nielsverhoeven/magewell-converter-cases/knowledge/neutrik/assets/README.md

# Neutrik drawings and 3D models (third-party assets)

Downloaded on 2026-09-07 from the public "Downloads" sections of neutrik.com product pages. Copyright Neutrik AG; stored here for engineering reference only (cutout geometry, depth behind panel, connector envelopes). Always use the black `-B` variant of each part in this project.

| File | Part | Source URL |
|---|---|---|
| NE8FDP-drawing.pdf / .dxf, NE8FDP.stp | etherCON NE8FDP(-B) | https://www.neutrik.com/media/8668/download/ne8fdp-3.pdf , https://www.neutrik.com/media/12095/download/ne8fdp-4.dxf , https://www.neutrik.com/media/12094/download/30010088_-_NE8FDP.stp |
| NAUSB-W-drawing.pdf / .dxf, NAUSB-W.stp | USB NAUSB-W(-B) | https://www.neutrik.com/media/8974/download/nausb-w-2.pdf , https://www.neutrik.com/media/12188/download/nausb-w-3.dxf , https://www.neutrik.com/media/16360/download/3D%20File%20NAUSB-W-A.stp |
| NAHDMI-W-drawing.pdf / .dxf, NAHDMI-W.stp | HDMI NAHDMI-W(-B) | https://www.neutrik.com/media/8976/download/Drawing%20NAHDMI-W.pdf , https://www.neutrik.com/media/12191/download/Drawing%20NAHDMI-W.dxf , https://www.neutrik.com/media/12190/download/nahdmi.stp |
| NBB75DFG-drawing.pdf / .dxf | BNC NBB75DFG(B) | https://www.neutrik.com/media/8619/download/nbb75dfg-2.pdf , https://www.neutrik.com/media/12043/download/nbb75dfg-3.dxf |
| NBB75DFI.stp | BNC isolated NBB75DFI(B) | https://www.neutrik.com/media/12639/download/3-d-nbb75dfi.stp |
| DBA-BL-drawing.pdf, DBA-BL.stp | Blanking plate DBA-BL(-B) | https://www.neutrik.com/media/8479/download/dba-2.pdf , https://www.neutrik.com/media/19043/download/3D%20Model%20dba-bl.stp |
| NZPF-z-panel-frame-assembly.pdf | Z-panel rack frame assembly instruction (NOT the D cutout standard; kept for reference only) | https://www.neutrik.com/media/8082/download/d-shape-z-panel.pdf |

The D-size cutout dimensions are on each connector drawing (panel cutout view). STEP files open in FreeCAD; convert to STL to use as a ghost body in OpenSCAD (see the `openscad-render` skill).
