nielsverhoeven/magewell-converter-cases/docs/plans/2026-09-28-wide-dovetail.md

# Plan A — wide dovetail with lock (rev 2), post-D34/D35 baseline

> **Implemented as amended by the architect verdict appended at the end of this file (B1–B17 and Amendment 1). Where they conflict, the verdict wins. §6 (lock) is informational only.**

Status: draft, NOT yet architect-validated. Route through `solution-architect` before any developer
starts.

Repo state: `main` @ `047902e`. Rev 2 supersedes rev 1 entirely (same file, overwritten) per user
decisions of 2026-09-28, relayed by the teamlead. **Section 6 (the lock) is a deliberate placeholder**
— do not implement it; the teamlead will resume this plan once a parallel researcher's analysis of
Christopher's DP48 STEP files lands.

**User decisions this revision implements:**
1. Coupling stays the dovetail, with an added lock. No thumbscrews.
2. Width: intermediate, dovetail root width in the 60–70 mm range — value picked and justified below.
3. Drop `fishtail_reserve` AND `case_tripod_insert` (the D35 boss is already gone; this retires the
   reservation too) so the rail can cover the floor centre.
4. Clearance ≥ 0.5 mm on every non-bearing surface: flanks (0.57735 mm horizontal, unchanged from rev
   1) **and now also the groove roof** (taper top vs. groove ceiling) — rev 1's "0 mm roof gap is
   fine" call is overridden by explicit user instruction.
5. Place the rail near the device/case centre of mass in Y (R24 roll-moment resistance), re-checked
   against every floor/wall feature, both existing brackets, and the new vertical bracket.
6. Lock: placeholder only, pending DP48 analysis.

---

## 0. Numeric evidence and scope carried over from rev 1, still valid

- The **standoff fix** (§1 below) is unchanged from rev 1: remove `mcc_rail_male()`'s `MCC_FLOOR_T`
  pedestal, `male-local Z = female-local Z` identity, drop `+ MCC_FLOOR_T` from both brackets' mate
  transforms. All of rev 1 §1's reasoning and exact edits still apply and are repeated in §1 below
  with the roof-clearance interaction folded in.
- The **mated-intersection prototype** from rev 1 (a real CGAL/Manifold `intersection()` render
  returning "Current top level object is empty") is still valid evidence for the flank-clearance
  mechanism; re-run at the new width in §7 before treating this plan as verified — the numbers moved,
  the method didn't.
- **Hard-won lesson, repeat:** any manual epsilon-overlap cut in a prototype must grow the shape's
  height, not just translate it (`_mcc_rail_taper_eps()`'s own pattern) — a bare Z-shift produced a
  false non-empty intersection when this was checked in rev 1.

---

## 1. Standoff fix (unchanged from rev 1) + its interaction with the new roof clearance

### 1.1 Remove the pedestal

`mcc_rail_male()` (`lib/mcc/rail.scad:222-236`) unions a `MCC_FLOOR_T`-tall pedestal under the taper.
Delete it; the male becomes just the taper, standing directly on the bracket's flat top face at local
Z=0 (see §4 for why it is now shorter than `MCC_RAIL_DEPTH`, not equal to it).

**Exact edits to `lib/mcc/rail.scad`:**

1. In `mcc_rail_male()`'s `union()`: delete
   `cuboid([len, MCC_RAIL_MOUTH_W, MCC_FLOOR_T], anchor = BOTTOM);` entirely, and change
   `translate([0, 0, MCC_FLOOR_T]) _mcc_rail_taper(len);` to just calling the taper at Z=0 with the
   new, shorter male height (§4 gives the exact call).
2. `_mcc_rail_flank_extrude(z0, z1)`: change `zb = MCC_FLOOR_T;` to `zb = 0;`, with a comment that the
   "straight" branch now only ever fires for a leg reaching *down* into the consumer's plate
   (`z0 < 0`), since the pedestal segment it used to represent no longer exists.
3. `mcc_rail_female_cut()`'s notch: delete the `translate([0, 0, -MCC_FLOOR_T])` wrapper (was
   compensating for the old `male Z = female Z + MCC_FLOOR_T` relationship — now `male Z = female Z`,
   identity, no compensation needed). See §4 for the exact new Z-range (it is not simply
   `[-MCC_EPS, MCC_RAIL_DEPTH]` any more, because of the roof clearance).
4. The latch-height assert (was `MCC_RAIL_SILL_H + plate_t >= 5`): change to reference the male's
   *actual* new height, `MCC_RAIL_MALE_H` (§4) — `MCC_RAIL_SILL_H` (7.0) stays the *case-side* sill
   height (T1-38, unrelated to the bracket) and must not be reused here.
5. Rewrite the stale header block (lines 35-43): no more pedestal/standoff language; state the local
   Z=0 correspondence is direct on both halves, and that the flat case-floor and flat bracket-plate
   faces, everywhere outside the two footprints, sit flush by construction.

**`lib/mcc/mounts.scad` needs no change for the standoff fix** — confirmed again on rev 2: every
`MCC_RAIL_SILL_H` reference there (`mcc_floor_features_add()`'s sill block, the D34 passage's
`pass_h` cap) is already case-side and untouched by the male's own pedestal.

### 1.2 Both bracket mate transforms drop `+ MCC_FLOOR_T`

- **`models/brackets/tv-bracket.scad:236`**: `translate([0, MCC_RAIL_Y, MCC_FLOOR_T]) rotate(...)` →
  `translate([0, MCC_RAIL_Y, 0]) rotate(...)`. Rewrite the "Derivation of the rotate([0,0,180])"
  comment block (lines 39-57) to the simpler, offset-free composition.
- **`models/brackets/arch-tv-bracket.scad`**: see §5 — bound up with the sweep-condition re-derivation,
  not a standalone edit.
- **`models/coupons/rail-latch.scad`**: no edit — it only calls the two public rail functions, so both
  fixes are picked up automatically. Its golden moves (§7).

---

## 2. Retire `fishtail_reserve` and `case_tripod_insert`

### 2.1 What to delete

**`lib/mcc/layout.scad`, `mcc_floor_keepout()`:** delete both rows —
```
[floor_center[0], floor_center[1], "circle", MCC_CASE_INSERT_KEEPOUT_D, "case_tripod_insert"],
[floor_center[0], floor_center[1], "rect", MCC_FISHTAIL_BAND, "fishtail_reserve"],
```
and the now-unused `floor_center = [0, 0]` local (nothing else in this function reads it once both
rows are gone — confirm with a grep before deleting, but tracing the current code, this is its only
use).

**`lib/mcc/mounts.scad`, `mcc_assert_floor_keepout_no_overlap()`:** delete the now-dead exemption
clause for the `"case_tripod_insert"`/`"fishtail_reserve"` pair (D19) — both labels can never appear
in the list again, so the `if (!((rows[i][4] == "case_tripod_insert" && ...) || ...))` wrapper around
the assert becomes unreachable dead code. Simplify back to a plain, unconditional pairwise assert.

**`lib/mcc/constants.scad`:** delete `MCC_CASE_INSERT_KEEPOUT_D` and `MCC_FISHTAIL_BAND` — both become
fully unused once their only consumer (the two rows above) is gone. Verify with
`grep -rn "MCC_CASE_INSERT_KEEPOUT_D\|MCC_FISHTAIL_BAND" lib/ models/ tests/` before deleting; if
either has grown a second consumer since this research pass, stop and report rather than deleting
silently.

### 2.2 `cfg["tripod_insert"]` — recommend assert-incompatible, not full retirement

The D35 boss (`mcc_case_tripod_insert_boss()`/`mcc_tripod_insert_bore_cut()` in `lib/mcc/cradle.scad`,
opt-in via `cfg["tripod_insert"]`, default `false` since D35) is **not itself removed by this plan** —
only the always-on floor *reservation* for it is. Recommendation: **make `tripod_insert=true` and
`rail=true` mutually exclusive by assert**, not delete the boss capability outright.

Reasoning for recommending this over full retirement: nothing currently ships with
`tripod_insert=true` (D35's default is already `false`), so there is no live regression either way.
Deleting the boss/bore modules and their T1-32/T1-41 asserts is real, working, tested code with no
compensating benefit today — it forecloses a genuine future option (a non-bracket-mounted variant that
still wants a floor tripod thread) for zero present gain. An assert is cheap, reversible, and states
the real physical fact plainly: with the rail now covering the floor centre, the two features cannot
coexist. If the architect judges the future-optionality argument not worth carrying, full retirement
(deleting `mcc_case_tripod_insert_boss()`/`_bore_cut()`, their call sites in `cradle.scad`, the
`tripod_insert` cfg key from all 8 `case.scad` files, and `MCC_INSERT_1_4_20` if it becomes unused) is
the documented alternative — flagged for the architect to pick, not silently assumed.

**Exact edit, `lib/mcc/cradle.scad`, `mcc_cradle()`** (where `tripod_on` is read): add, right after the
existing `tripod_on = is_undef(tripod_flag) ? false : tripod_flag;` line —
```
assert(!(tripod_on && struct_val(cfg, "rail") != false),
    "mcc: cfg[\"tripod_insert\"]=true cannot combine with the mount rail (cfg[\"rail\"], default "
    + "true) -- the rail now covers the floor centre the tripod insert boss needs (2026-09-28 "
    + "wide-dovetail decision). Set [\"rail\", false] to use the tripod insert instead.");
```
(`struct_val(cfg, "rail") != false` mirrors the same `is_undef(...) ? true : ...` default the rail
flag itself uses elsewhere, so an *absent* `"rail"` key — which defaults to rail-on — correctly still
trips this assert.)

### 2.3 `CLAUDE.md`'s fixed-decision floor-features line

This file is project-owned prose, not something this plan edits — proposed replacement text for
whoever applies it (the current line is already stale, predating D-15's VESA removal):

> Floor features (one owner, `mounts.scad`): the tool-less dovetail mount rail (default; see §11 D-xx
> for width/placement), strap slots, splitter tie-down, stacking profile. The case's own 1/4"-20
> threaded insert is an **opt-in alternative to the rail**, mutually exclusive with it (assert-guarded,
> `cradle.scad`), not fitted by default. VESA 75×75 (D-15) and Magewell-Fishtail M4 compatibility
> (2026-09-28 wide-dovetail decision) have both been dropped — the rail now needs the floor centre they
> used to reserve.
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
