nielsverhoeven/magewell-converter-cases/tests/test_rail.scad

//////////////////////////////////////////////////////////////////////
// tests/test_rail.scad
//   Tier-2 headless smoke test (architecture.md §9). Instantiates every public module/function in
//   lib/mcc/rail.scad at default (MCC_RAIL_LEN) and short (coupon-scale, len=60) parameters, and
//   exercises the two rev-9 blocking asserts issue #25 introduced:
//     - T1-38 (lib/mcc/rail.scad mcc_rail_female_cut()): >= MCC_FLOOR_T of residual floor over the
//       groove (layout-patch-wall.md §17.2 R1).
//     - D16 (lib/mcc/mounts.scad mcc_assert_floor_keepout_no_overlap()): no two
//       mcc_floor_keepout() rows overlap (no exemptions since D44), run against a real device record.
//     - T1-63.1 .. T1-63.3 (D63.1): the top lock's ride budget, strips and roof lead-in; D50: the
//       rail's plate-side keep-out, mcc_rail_male_keepout().
//     - T1-64.1 (D64.1): the groove's closed -X end keeps a full end wall; T1-17 (D45/D64.1): the rail sill
//       clears the reserved splitter bay, against the tightest SKU (L = 193.9).
//     - T1-62 (D44): >= MCC_RAIL_MATE_CLR normal to the flanks and at the roof.
//   CSG export (-o out.csg) evaluates the full tree so in-model asserts fire, without tessellating.
// Run:
//   openscad --backend=Manifold -o out.csg tests/test_rail.scad
//////////////////////////////////////////////////////////////////////

$fa = 1; $fs = 0.4;

include <mcc/mcc.scad>
include <mcc/devices/pro-convert-for-ndi-to-hdmi.scad>

// --- mcc_rail_sill_size() -- pure function, no geometry ----------------------------------------
_sill = mcc_rail_sill_size();
assert(_sill[0] == MCC_RAIL_LEN + 2 * MCC_RAIL_END_WALL, str("mcc_rail_sill_size len=", _sill[0]));
assert(_sill[1] == MCC_RAIL_ROOT_W + 2 * MCC_RAIL_SILL_SIDE_W, str("mcc_rail_sill_size width=", _sill[1]));
// D30: the sill's side walls beside the groove root must be real walls, not knife edges.
assert(MCC_RAIL_SILL_SIDE_W >= MCC_WALL - MCC_EPS, str("D30: MCC_RAIL_SILL_SIDE_W=", MCC_RAIL_SILL_SIDE_W, " below MCC_WALL"));
assert(_sill[2] == MCC_RAIL_SILL_H, str("mcc_rail_sill_size height=", _sill[2]));

// --- T1-38: MCC_RAIL_SILL_H - MCC_RAIL_DEPTH >= MCC_FLOOR_T, checked directly (not just via the
// module assert, which only fires at render) so a constants.scad regression fails this smoke test
// with a clear message before it ever reaches a full case render. ----------------------------
assert(MCC_RAIL_SILL_H - MCC_RAIL_DEPTH >= MCC_FLOOR_T,
    str("T1-38: MCC_RAIL_SILL_H(", MCC_RAIL_SILL_H, ") - MCC_RAIL_DEPTH(", MCC_RAIL_DEPTH,
        ") must be >= MCC_FLOOR_T(", MCC_FLOOR_T, ")"));

// --- Top lock (D63.1): ride budget, strips and roof lead-in, checked from the constants so a regression
// fails here before any render (T1-63.1 .. T1-63.3, T1-64.1). ----------------------------------------------
assert(abs(mcc_rail_z_play() - MCC_RAIL_MATE_CLR / cos(MCC_RAIL_FLANK_ANGLE)) < 1e-6,
    str("mcc_rail_z_play()=", mcc_rail_z_play()));
assert(MCC_RAIL_LOCK_ENGAGE + MCC_RAIL_LOCK_PLAY_MARGIN <= mcc_rail_z_play() + MCC_EPS,
    str("T1-63.1: lock strip ", MCC_RAIL_LOCK_ENGAGE, " + margin ", MCC_RAIL_LOCK_PLAY_MARGIN,
        " does not fit the Z-play ", mcc_rail_z_play()));
assert(30 <= MCC_RAIL_LOCK_RAMP_IN && MCC_RAIL_LOCK_RAMP_IN <= 60, "T1-63.2: lock entry chamfer outside 30..60 deg");
assert(MCC_RAIL_LOCK_STRIP_Y_OUT <= MCC_RAIL_MOUTH_W / 2 + MCC_RAIL_MALE_H / tan(MCC_RAIL_FLANK_ANGLE) - 1,
    "T1-63.2: lock strips reach within 1 mm of the male's top edge");
assert(MCC_RAIL_LOCK_ENGAGE < MCC_RAIL_LEADIN && MCC_RAIL_LEADIN <= MCC_WALL,
    "T1-63.3: rail lead-in not taller than the lock engagement, or deeper than MCC_WALL");
assert(MCC_RAIL_END_WALL >= MCC_WALL - MCC_EPS, "T1-64.1: the groove's closed end wall is thinner than MCC_WALL");
_slot = mcc_rail_lock_slot();
assert(_slot[1] == [-(MCC_RAIL_ROOT_W / 2 + MCC_RAIL_CLR_HORIZ), MCC_RAIL_ROOT_W / 2 + MCC_RAIL_CLR_HORIZ],
    str("D63.1: the lock slot must span the whole roof, got y=", _slot[1]));
assert(abs(_slot[2][1] - (MCC_RAIL_DEPTH + MCC_RAIL_LOCK_ENGAGE + MCC_RAIL_ROOF_CLR)) < 1e-6,
    str("D63.1: lock slot ceiling z=", _slot[2][1]));

// --- D50: the plate-side keep-out every bracket reads (never the MCC_RAIL_LOCK_* constants) --------
_rail_ko = mcc_rail_male_keepout();
assert(_rail_ko == [[-MCC_RAIL_LEN / 2, MCC_RAIL_LEN / 2],
                    [-MCC_RAIL_ROOT_W / 2, MCC_RAIL_ROOT_W / 2]],
    str("D50: mcc_rail_male_keepout()=", _rail_ko));
assert(mcc_rail_male_keepout(60)[0] == [-30, 30],
    str("D50: mcc_rail_male_keepout(60)=", mcc_rail_male_keepout(60)));

// --- T1-62 / D44: >= MCC_RAIL_MATE_CLR on every non-bearing face, and the user's width range ------
assert(MCC_RAIL_CLR_HORIZ * sin(MCC_RAIL_FLANK_ANGLE) >= MCC_RAIL_MATE_CLR - MCC_EPS,
    str("T1-62: rail flank clearance ", MCC_RAIL_CLR_HORIZ * sin(MCC_RAIL_FLANK_ANGLE), " below ", MCC_RAIL_MATE_CLR));
assert(MCC_RAIL_DEPTH - MCC_RAIL_MALE_H >= MCC_RAIL_MATE_CLR - MCC_EPS,
    str("T1-62: rail roof clearance ", MCC_RAIL_DEPTH - MCC_RAIL_MALE_H, " below ", MCC_RAIL_MATE_CLR));
assert(MCC_RAIL_MATE_CLR >= 0.5 - MCC_EPS, "D44: the user's minimum rail clearance is 0.5 mm");
assert(MCC_RAIL_ROOT_W >= 60 && MCC_RAIL_ROOT_W <= 70,
    str("D44: MCC_RAIL_ROOT_W=", MCC_RAIL_ROOT_W, " outside the user's 60-70 mm range"));

// --- mcc_rail_male() / mcc_rail_female_cut() -- default (production MCC_RAIL_LEN) --------------
translate([0, 0, 0]) mcc_rail_male();
// D50: a consumer unions the rail onto its plate -- the rail needs no cut in the plate.
translate([0, -60, 0])
    union() {
        translate([0, 0, -6]) cuboid([MCC_RAIL_LEN + 10, MCC_RAIL_ROOT_W + 10, 6], anchor = BOTTOM);
        mcc_rail_male();
    }
translate([0, 60, 0])
    difference() {
        cuboid([MCC_RAIL_LEN, MCC_RAIL_ROOT_W + 20, MCC_RAIL_SILL_H], anchor = BOTTOM);
        mcc_rail_female_cut(open_ext = 20, entry_x = MCC_RAIL_LEN / 2);
    }

// --- mcc_rail_male() / mcc_rail_female_cut() -- short, coupon-scale len=60 (models/coupons/
// rail-lock.scad's own length) -- the lock strips must be re-derived from THIS len
// (len/2 - MCC_RAIL_LOCK_END_OFFSET); this is exactly the regression the len=60 case here guards
// against. The e-ladder's largest strip (lock_e = 0.7, M15; T1-63.1's ceiling) must render too, with
// its backing. ------------------------------------------------------------------------------------
translate([200, 0, 0]) mcc_rail_male(len = 60);
translate([200, 60, 0])
    difference() {
        cuboid([60, MCC_RAIL_ROOT_W + 20, MCC_RAIL_SILL_H], anchor = BOTTOM);
        mcc_rail_female_cut(len = 60);
    }
translate([300, 0, 0]) mcc_rail_male(len = 60, lock_e = 0.7);
translate([300, 60, 0])
    difference() {
        union() {
            cuboid([62, MCC_RAIL_ROOT_W + 20, MCC_RAIL_SILL_H], anchor = BOTTOM);
            mcc_rail_female_backing(len = 60, lock_e = 0.7);
        }
        mcc_rail_female_cut(len = 60, open_ext = 1, entry_x = 31, lock_e = 0.7);
    }

// --- D16 / D19 (lib/mcc/mounts.scad): pairwise floor-keepout non-overlap, against a real device
// record and its default variant config, with the mount-rail row now in the list. Emits no
// geometry (pure assert module) -- a bare module-call statement is enough to force evaluation.
DEV = MCC_DEV_PRO_CONVERT_FOR_NDI_TO_HDMI;
VARIANT = [
    ["fan",      false],
    ["splitter", false],
];
mcc_assert_floor_keepout_no_overlap(DEV, VARIANT);

// mcc_floor_keepout()'s own "mount_rail" row, sanity-checked directly (rev 9, D-15).
_ko = mcc_floor_keepout(DEV, VARIANT);
_rail_rows = [for (r = _ko) if (r[4] == "mount_rail") r];
assert(len(_rail_rows) == 1, str("expected exactly one \"mount_rail\" row, got ", len(_rail_rows)));
// D34: the groove runs from its closed end at -MCC_RAIL_LEN/2 out through the +X wall.
_L = struct_val(mcc_case_layout(DEV, VARIANT), "L");
assert(abs(_rail_rows[0][0] - (_L / 2 - MCC_RAIL_LEN / 2) / 2) < 1e-6 && _rail_rows[0][1] == MCC_RAIL_Y,
    str("mount_rail row centre=", [_rail_rows[0][0], _rail_rows[0][1]]));
assert(_rail_rows[0][3] == [_L / 2 + MCC_RAIL_LEN / 2, MCC_RAIL_ROOT_W],
    str("mount_rail row size=", _rail_rows[0][3]));
// No "vesa_*" rows survive (D-15 -- VESA fully removed, not deprecated-but-optional).
_vesa_rows = [for (r = _ko) if (r[4] == "vesa_ne" || r[4] == "vesa_se" || r[4] == "vesa_nw" || r[4] == "vesa_sw") r];
assert(len(_vesa_rows) == 0, str("expected zero VESA rows, got ", len(_vesa_rows)));

// --- mcc_floor_features_add()/mcc_rail_features_cut() -- the shell.scad call-site pair, exercised
// directly (default cfg["rail"]=true) so the ADD/CUT split renders as one clean, watertight block.
translate([400, 0, 0])
    difference() {
        mcc_floor_features_add(DEV, VARIANT);
        mcc_rail_features_cut(DEV, VARIANT);
    }

// cfg["rail"]=false -- both must render (and add/cut) nothing, not error.
translate([400, 60, 0]) {
    mcc_floor_features_add(DEV, [["fan", false], ["splitter", false], ["rail", false]]);
    mcc_rail_features_cut(DEV, [["fan", false], ["splitter", false], ["rail", false]]);
}

echo("mcc test_rail: OK");

// -----------------------------------------------------------------------------------------
// Manual checks: OpenSCAD has no "expect this render to fail" mechanism, so these cannot be
// asserted automatically in a render that must otherwise succeed. To verify a guard by hand,
// append the indicated line to a scratch copy of this file and confirm the render FAILS
// (non-zero exit) with an ERROR containing the quoted text.
//
// 1. T1-38, violated directly by shrinking the constant (constants.scad would need a local
//    override, e.g. via -D, since MCC_RAIL_SILL_H is derived -- simplest is a scratch edit setting
//    MCC_RAIL_SILL_H = MCC_RAIL_DEPTH + 1.0 in constants.scad and re-running this file):
//    -> "T1-38: MCC_RAIL_SILL_H(5) - MCC_RAIL_DEPTH(4) must be >= MCC_FLOOR_T(3)"
//
// 2. D16, violated by moving the rail onto the side-bolt support web (scratch edit constants.scad
//    MCC_RAIL_Y = -40):
//    -> "mcc: floor features \"mount_rail\" and \"side_bolt_web\" overlap ... (D16)"
//
// 3. T1-63 (D44), the opt-in case insert together with the (default-on) rail:
//    mcc_cradle(DEV, [["fan", false], ["splitter", false], ["tripod_insert", true]]);
//    -> "mcc: T1-63 cfg[\"tripod_insert\"]=true needs [\"rail\", false] ..."
//
// 4. T1-63.1 (D63.1), lock strips too tall for the Z-play (scratch edit constants.scad
//    MCC_RAIL_LOCK_ENGAGE = 0.8), then render a case base or the coupon; the render fails with:
//    "mcc: T1-63.1 rail lock strip 0.8 + margin 0.3 does not fit the Z-play 1"
//
// 5. T1-17 (D64.1), the rail sill running into the splitter bay (scratch edit constants.scad
//    MCC_RAIL_LEN = 150.0), then run this file; it fails with:
//    "mcc: T1-17 rail sill -X end x=-78 is within MCC_FAN_BAY_CLR=2 of the reserved splitter bay ..."
// -----------------------------------------------------------------------------------------

// vim: expandtab tabstop=4 shiftwidth=4 softtabstop=4 nowrap
