nielsverhoeven/magewell-converter-cases/tests/test_shell.scad

//////////////////////////////////////////////////////////////////////
// tests/test_shell.scad
//   Tier-2 headless smoke test (architecture.md §9). Instantiates mcc_shell_base()/
//   mcc_shell_lid() (shell.scad), mcc_cradle() (cradle.scad), mcc_floor_features_add/cut()
//   (mounts.scad), and mcc_vents() for each of the 3 vented wall faces (vents.scad), all for
//   MCC_DEV_PRO_CONVERT_FOR_NDI_TO_HDMI — CSG export (-o out.csg) evaluates the full tree so every
//   in-model Tier-1 assert fires, without tessellating. Also exercises the lid vent field (issue
//   #24, T1-36/T1-37) via VARIANT/VARIANT_FAN (lid_vents=true) and VARIANT_NO_LID_VENTS
//   (lid_vents=false).
// Run:
//   openscad --backend=Manifold -o out.csg tests/test_shell.scad
//////////////////////////////////////////////////////////////////////

$fa = 1; $fs = 0.4;

include <mcc/mcc.scad>
include <mcc/devices/pro-convert-for-ndi-to-hdmi.scad>
include <mcc/devices/pro-convert-hdmi-plus.scad>

DEV = MCC_DEV_PRO_CONVERT_FOR_NDI_TO_HDMI;
// "external_ports" is DROPPED from cfg (D12, architecture.md §13 -- inert, never implemented; the
// slot set comes solely from mcc_ports_external(dev)). Real cfg keys only.
VARIANT = [
    ["fan",             false],
    ["splitter",        false],
    ["lid_vents",       true],
];
VARIANT_FAN = [
    ["fan",             true],
    ["splitter",        false],
    // ["fan_switch",false]: the compact family's feasible switch_y interval is EMPTY (D-18,
    // layout-patch-wall.md §18.2) -- without this, T1-43 fails on this SKU's own base_fan golden.
    ["fan_switch",      false],
];

// Fan-switch coverage (rev 11, #32, D-18 §18.4): B6 stops the compact VARIANT_FAN above from
// exercising the switch cutout at all, so without a plus-family branch the feature would ship
// untested by `smoke` (D15's lesson, repeated). DEV_PLUS/VARIANT_PLUS_SWITCH exist ONLY to give
// mcc_switch_cutout()/mcc_switch_pad() and T1-43/T1-44 a real render-time exercise.
DEV_PLUS = MCC_DEV_PRO_CONVERT_HDMI_PLUS;
VARIANT_PLUS_SWITCH = [
    ["fan",             true],
    ["splitter",        false],
    ["fan_switch",      true],
    ["lid_vents",       true],
];
// tripod_insert defaults to false (D35) when the key is absent, as VARIANT/VARIANT_FAN above both
// exercise implicitly. This variant explicitly sets it false, exercising the deck-lattice's
// tripod_insert=false path (issue #29) -- the boss and its collar/bore-cut are omitted entirely.
VARIANT_NO_TRIPOD = concat(VARIANT, [["tripod_insert", false]]);
// Explicit lid_vents=false render (issue #24) -- exercises mcc_shell_lid()'s gate so a broken
// default-true fallback would still be caught here even if every other VARIANT* left it implicit.
VARIANT_NO_LID_VENTS = concat(VARIANT, [["lid_vents", false]]);

// --- shell.scad: both halves, default (fan=false) variant ---
mcc_shell_base(dev = DEV, cfg = VARIANT);
translate([0, 250, 0]) mcc_shell_lid(dev = DEV, cfg = VARIANT);

// --- shell.scad: lid with lid_vents=false (issue #24 -- comparison/gate check) ---
translate([0, 750, 0]) mcc_shell_lid(dev = DEV, cfg = VARIANT_NO_LID_VENTS);

// --- shell.scad: base with fan=true (exercises the fan-cutout branch) ---
translate([250, 0, 0]) mcc_shell_base(dev = DEV, cfg = VARIANT_FAN);

// --- shell.scad: plus-family base with fan=true + fan_switch=true (exercises the switch cutout) ---
translate([1000, 0, 0]) mcc_shell_base(dev = DEV_PLUS, cfg = VARIANT_PLUS_SWITCH);

// --- shell.scad: plus-family lid (T1-62.1/T1-62.2 on both families) ---
translate([1000, 250, 0]) mcc_shell_lid(dev = DEV_PLUS, cfg = VARIANT_PLUS_SWITCH);

// --- cradle.scad standalone ---
// --- shell.scad: base with tripod_insert=false (issue #29 -- boss/collar/bore-cut all omitted) ---
translate([250, 500, 0]) mcc_shell_base(dev = DEV, cfg = VARIANT_NO_TRIPOD);
// --- cradle.scad standalone (default tripod_insert=false, D35; true needs ["rail", false], T1-63) ---
translate([250, 250, 0]) mcc_cradle(dev = DEV, cfg = VARIANT);

// --- mounts.scad standalone ---
translate([500, 0, 0]) mcc_floor_features_add(dev = DEV, cfg = VARIANT);

// --- vents.scad standalone, all 3 vented faces + area sanity ---
l = mcc_case_layout(DEV, VARIANT);
W = struct_val(l, "W");
area = mcc_vent_intake_area(DEV, VARIANT);
echo(str("mcc test_shell: T1-30 net intake area=", area, " mm^2, threshold=",
    MCC_VENT_AREA_RATIO * PI / 4 * MCC_FAN_APERTURE_D * MCC_FAN_APERTURE_D, " mm^2"));
assert(area >= MCC_VENT_AREA_RATIO * PI / 4 * MCC_FAN_APERTURE_D * MCC_FAN_APERTURE_D,
    str("mcc test_shell: T1-30 net intake area ", area, " below threshold"));

// --- vents.scad: lid vent field area sanity (issue #24, T1-36) -- convenience echo only; the
// actual authority is the in-model assert inside mcc_lid_vents_cut() (called via mcc_shell_lid()
// above), same discipline the T1-30 block already follows for the wall vents (D15's lesson). ---
lid_area = mcc_lid_vent_area(DEV, VARIANT);
echo(str("mcc test_shell: T1-36 net lid vent area=", lid_area, " mm^2, threshold=",
    MCC_LID_VENT_AREA_RATIO * PI / 4 * MCC_FAN_APERTURE_D * MCC_FAN_APERTURE_D, " mm^2"));
assert(lid_area >= MCC_LID_VENT_AREA_RATIO * PI / 4 * MCC_FAN_APERTURE_D * MCC_FAN_APERTURE_D,
    str("mcc test_shell: T1-36 net lid vent area ", lid_area, " below threshold"));

translate([750, 0, 0])
    difference() {
        cube([200, W + 20, 60], center = false);
        translate([100, W / 2 + 10, 0]) mcc_vents(dev = DEV, cfg = VARIANT, face = [0, -1, 0]);
    }
translate([750, 250, 0])
    difference() {
        cube([200, W + 20, 60], center = false);
        translate([100, W / 2 + 10, 0]) mcc_vents(dev = DEV, cfg = VARIANT, face = [-1, 0, 0]);
    }
translate([750, 500, 0])
    difference() {
        cube([200, W + 20, 60], center = false);
        translate([100, W / 2 + 10, 0]) mcc_vents(dev = DEV, cfg = VARIANT_FAN, face = [1, 0, 0]);
    }

echo("mcc test_shell: OK");

// -----------------------------------------------------------------------------------------
// Manual check: mcc_vents() must reject the patch wall (T1-19). OpenSCAD has no "expect this
// render to fail" mechanism, so this cannot be asserted automatically in a render that must
// otherwise succeed. To verify by hand, append the following line to a scratch copy of this file
// and confirm the render FAILS with an ERROR containing "T1-19":
//
//   mcc_vents(dev = DEV, cfg = VARIANT, face = [0, 1, 0]);
//
// Manual check (T1-62.1/T1-62.2, D62.1), OPENSCADPATH=lib: force the old patch-wall frame and confirm FAIL:
//   openscad --backend=Manifold -D 'part="lid"' -D MCC_TG_PATCH_INSET=8 -o neg.csg models/pro-convert-hdmi-plus/case.scad
//   -> ERROR "T1-62.1 lid fastener [95.25, 73.175] countersink rim is -1.91441 mm from the groove ..."
//   -D MCC_TG_PATCH_INSET=2 instead (part "lid" or "base") -> ERROR "T1-62.2 MCC_TG_PATCH_INSET=2 outside [...]"
// -----------------------------------------------------------------------------------------

// vim: expandtab tabstop=4 shiftwidth=4 softtabstop=4 nowrap
